Lufteluke/pi-tin/images/3dp_case_closed.jpg

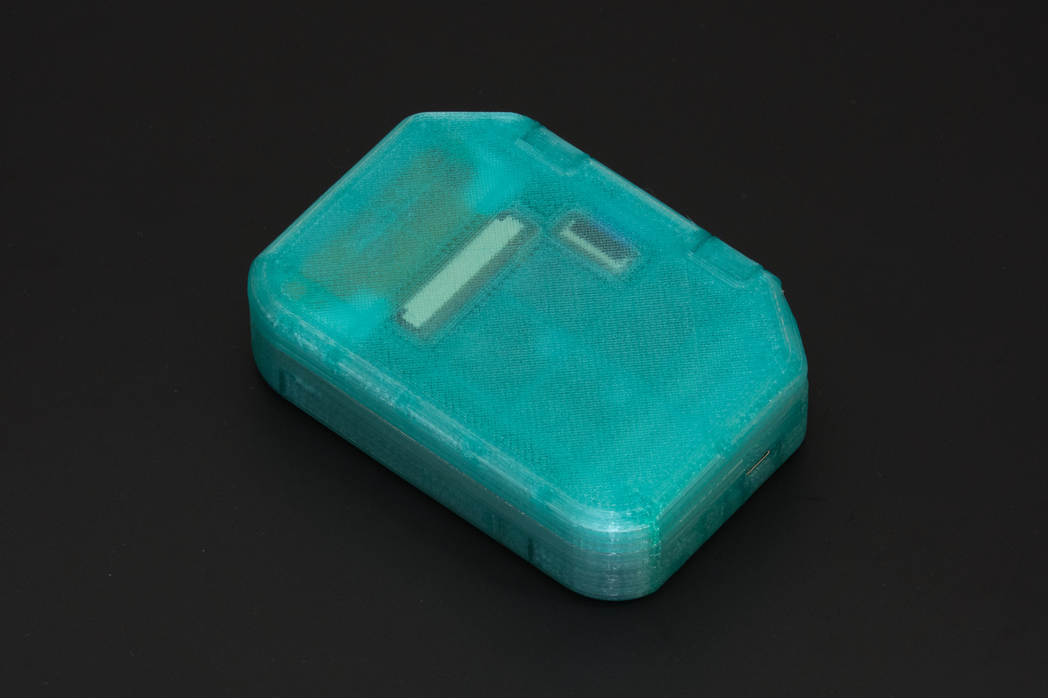
images/3dp_case_closed.jpg
