Lufteluke/pi-tin/images/alignment_bad_1.jpg

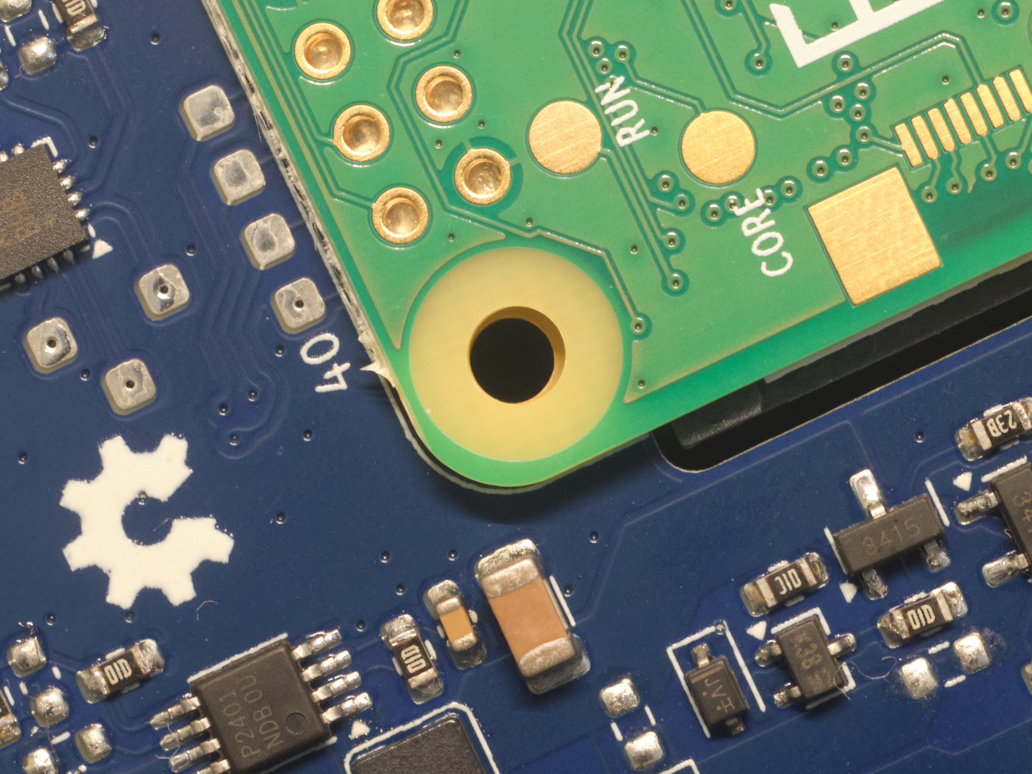
images/alignment_bad_1.jpg
