Lufteluke/pi-tin/images/alignment_bad_2.jpg

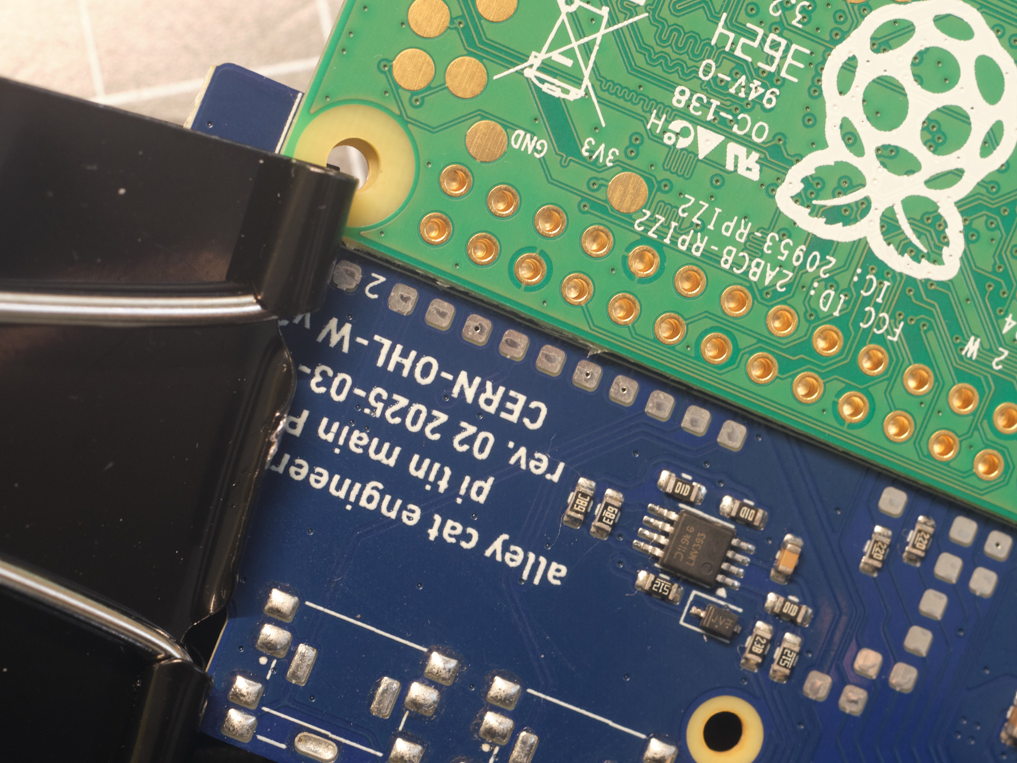
images/alignment_bad_2.jpg
