Lufteluke/pi-tin/images/alignment_good_1.jpg

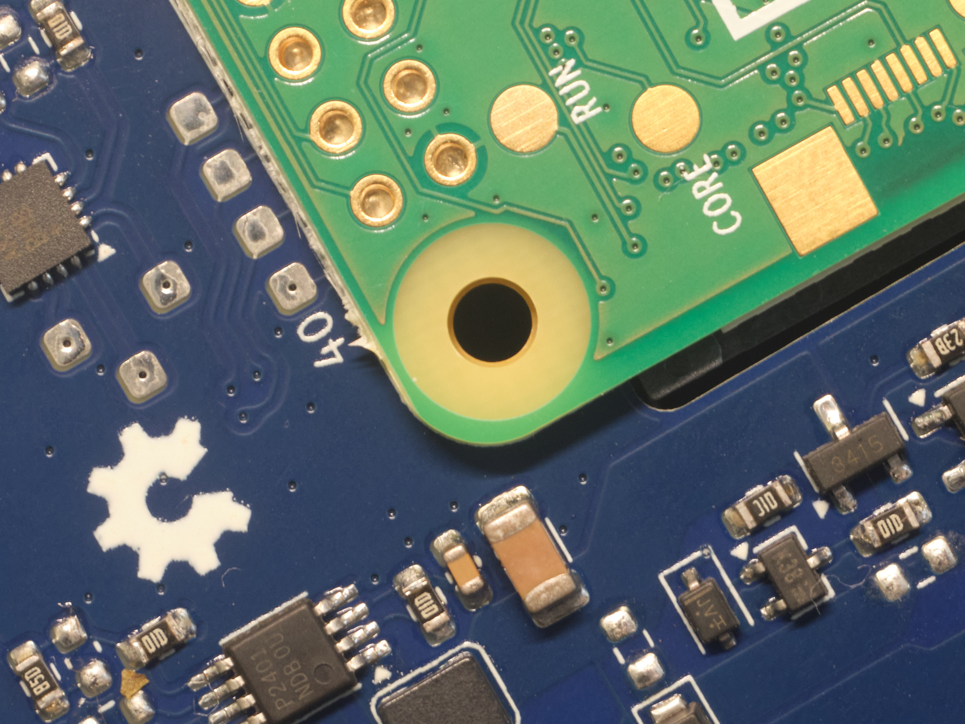
images/alignment_good_1.jpg
