Lufteluke/pi-tin/images/alignment_good_2.jpg

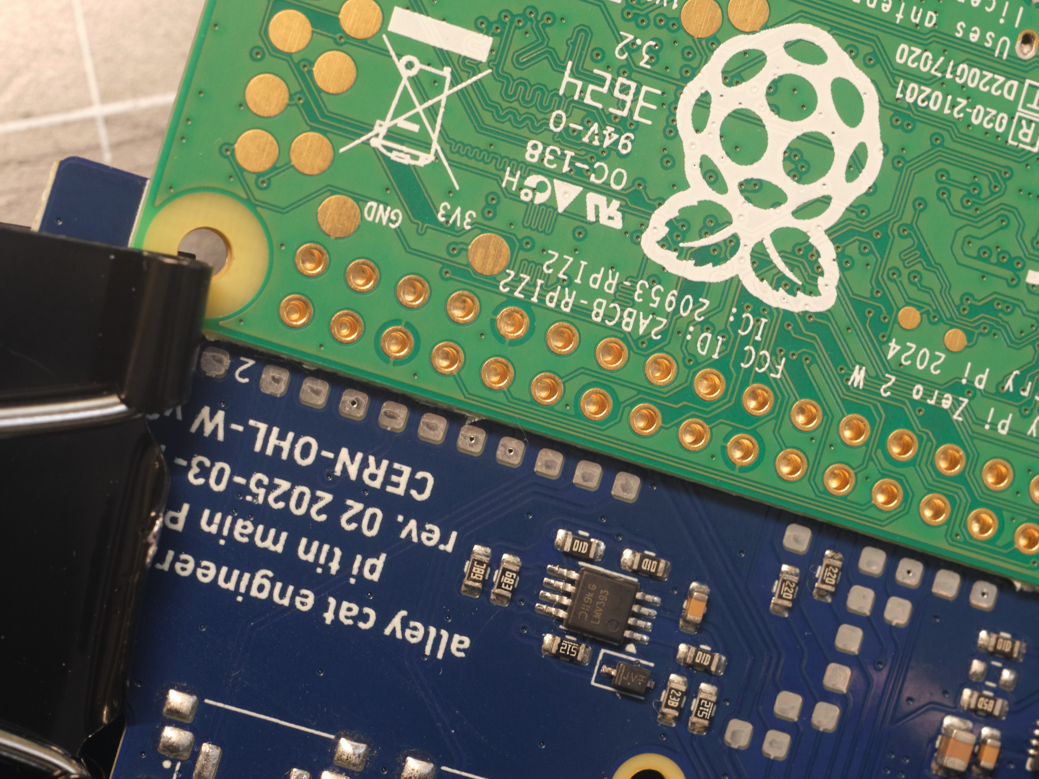
images/alignment_good_2.jpg
