Lufteluke/pi-tin/images/display_conn_after.jpg

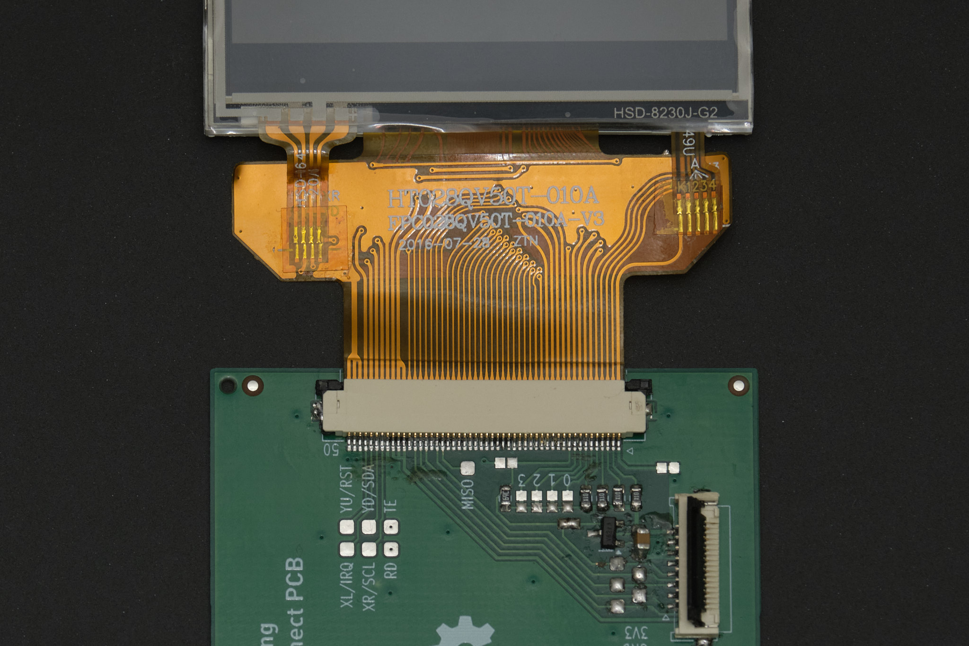
images/display_conn_after.jpg
