Lufteluke/pi-tin/images/display_conn_before.jpg

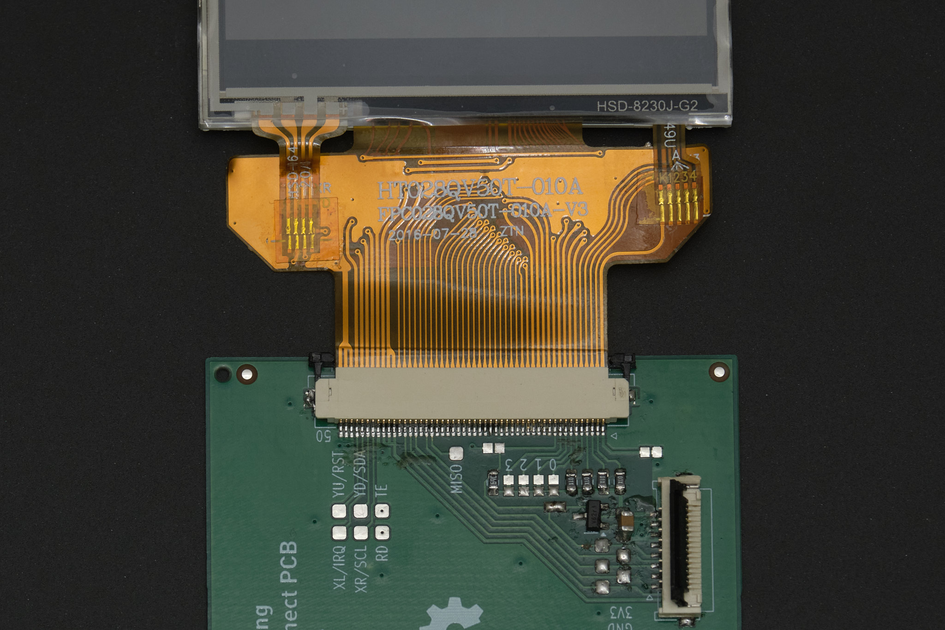
images/display_conn_before.jpg
