Lufteluke/pi-tin/images/display_pcb.jpg

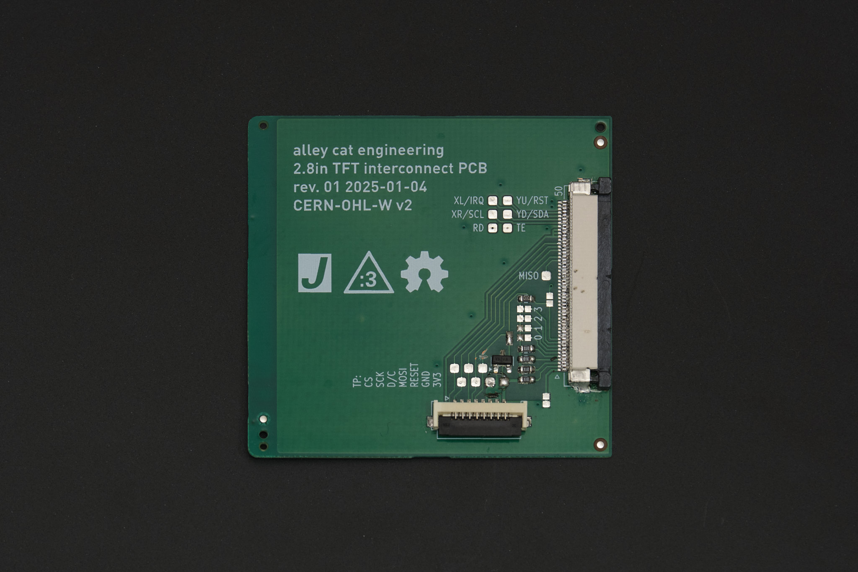
images/display_pcb.jpg
