Lufteluke/pi-tin/images/front_panel_front.png

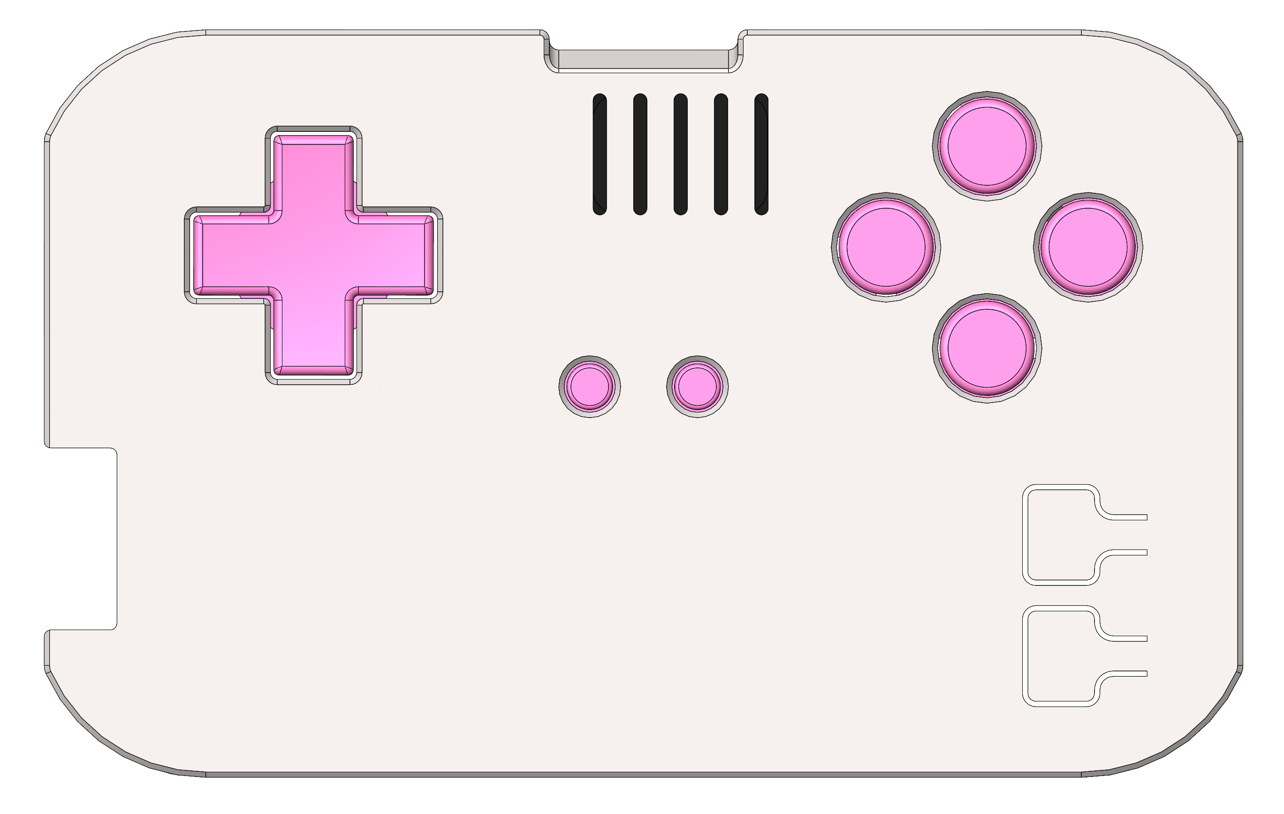
images/front_panel_front.png
