Lufteluke/pi-tin/images/hotkeys.png

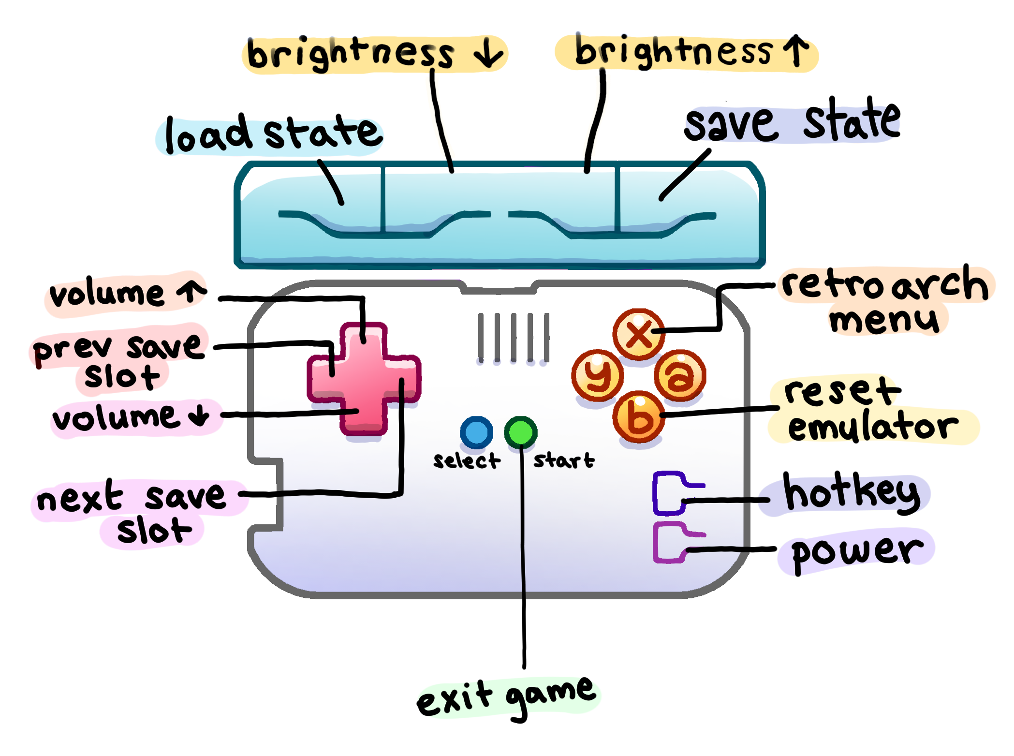
images/hotkeys.png
