Lufteluke/pi-tin/images/hotkeys_ref.png

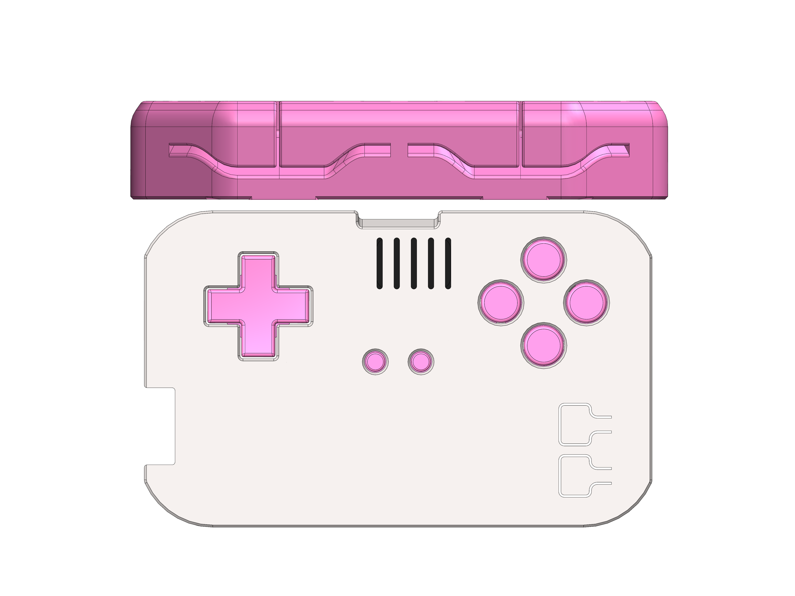
images/hotkeys_ref.png
