Lufteluke/pi-tin/images/incorrect_display_mount.png

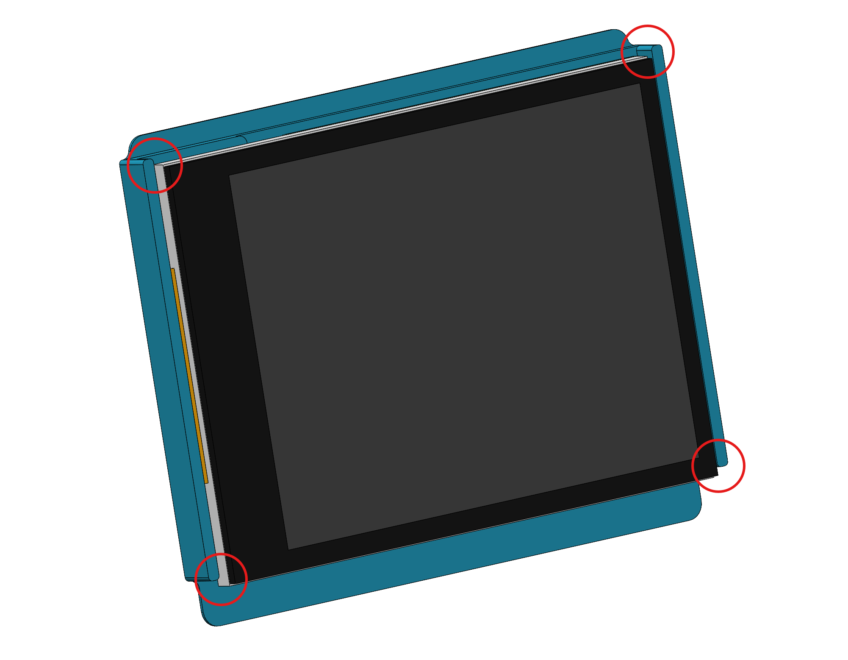
images/incorrect_display_mount.png
