Lufteluke/pi-tin/images/lid_holder_magnets.png

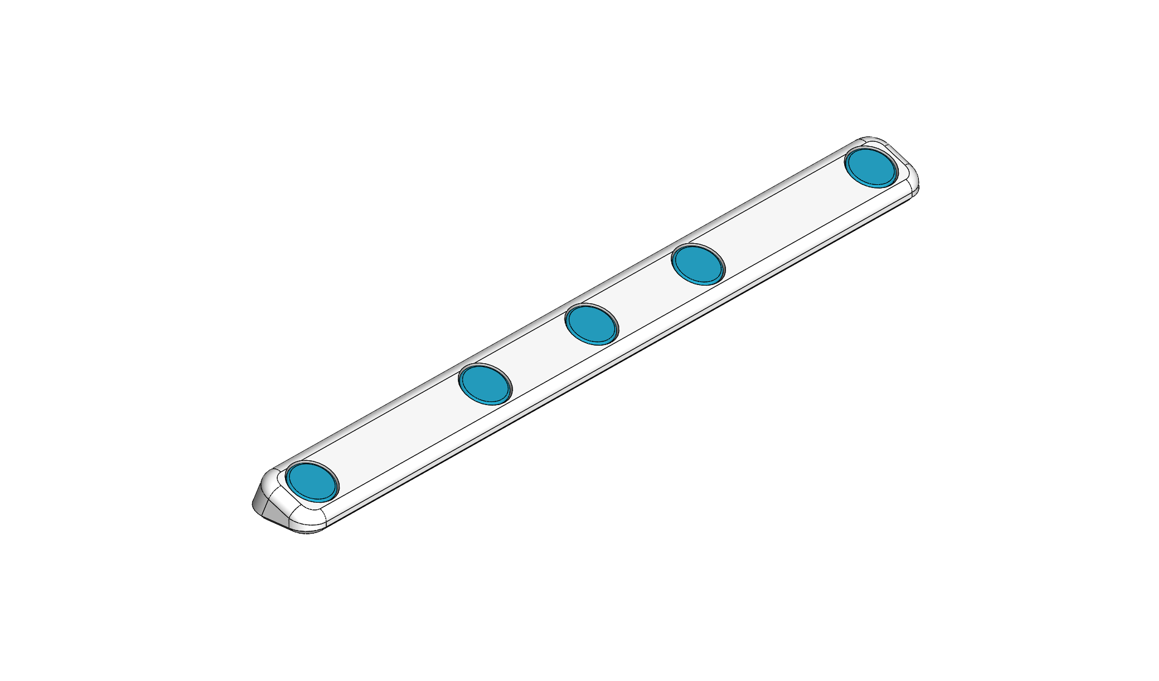
images/lid_holder_magnets.png
