Lufteluke/pi-tin/images/main_pcb_2.jpg

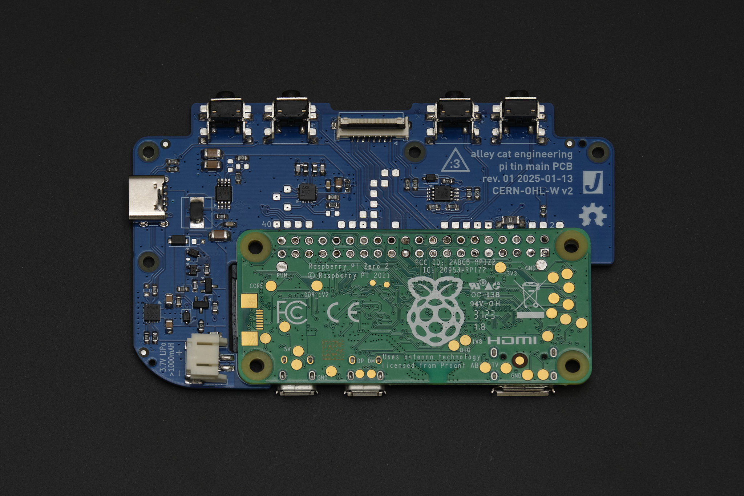
images/main_pcb_2.jpg
