Lufteluke/pi-tin/images/pcb_bare.png

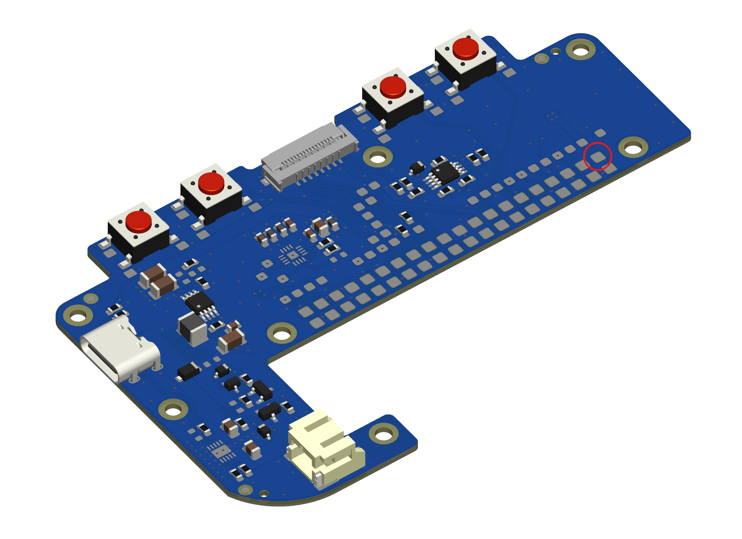
images/pcb_bare.png
