Lufteluke/pi-tin/images/pi_alignment.png

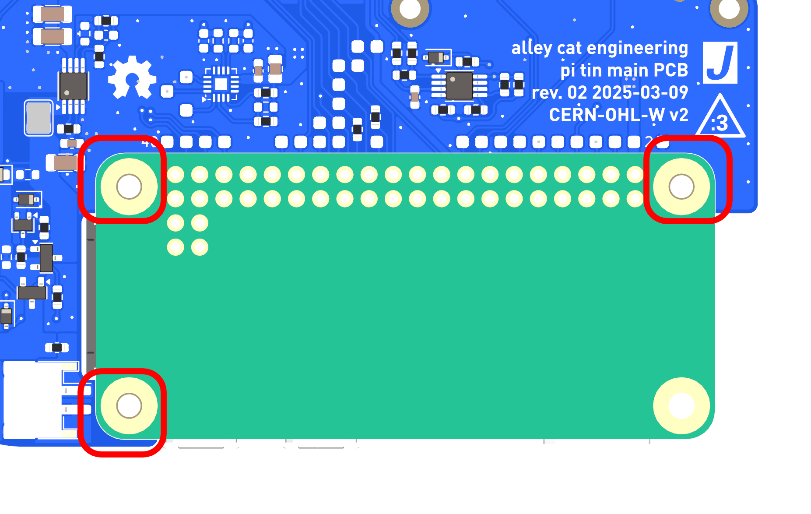
images/pi_alignment.png
