Lufteluke/pi-tin/images/rear_buttons.png

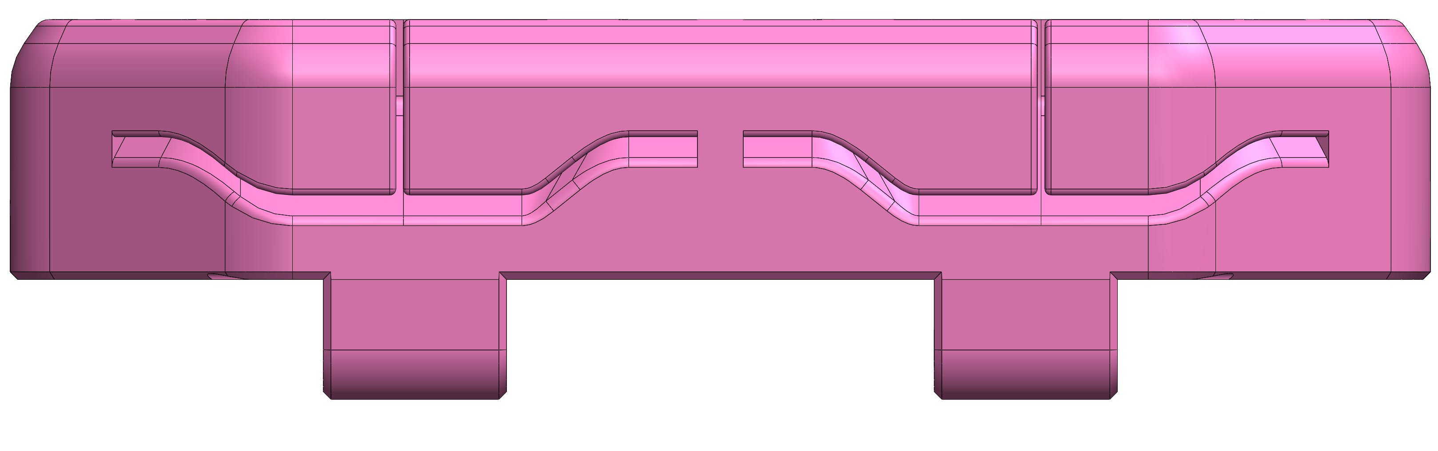
images/rear_buttons.png
